A1ej0/EMA/EMA_codigoMicro/Esp32/ajustes.py

Ajustes para conexion GRPS con MQTT:

apn:internet.comcel.com.co
host:138.128.244.81
puerto:1883
user:EMA
claveMqtt:SGCEMA

Ajustes wifi:

red:Alejo4G
clave:Alejo1993

Bluetooth:

nombre:EMA3.4

Telefonos:

Telefono1:3025823307
Telefono2:3123776985
Telefono3:3014961877

version:3.4
